MikaGS/Film_Scanning_Stand/3D files/drilling_jig.stp

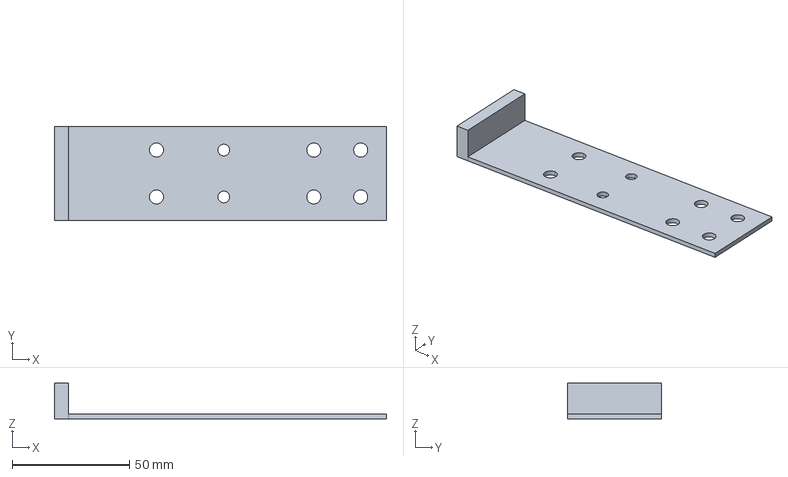
[picture p15: CAD file, 2026-05-22]
3D files/drilling_jig.stp
141.5 x 40.0 x 15.2 mm
